e7p/ledmatrix/board_ledmatrix/ledmatrix.c

/*
	ledramp.c
	
	Copyright 2008, 2009 Michel Pollet <buserror@gmail.com>

 	This file is part of simavr.

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
	You should have received a copy of the GNU General Public License
	along with simavr.  If not, see <http://www.gnu.org/licenses/>.
 */

#include <stdlib.h>
#include <stdio.h>
#include <libgen.h>
#if __APPLE__
#include <GLUT/glut.h>
#else
#include <GL/glut.h>
#endif
#include <pthread.h>

#include "sim_avr.h"
#include "avr_ioport.h"
#include "sim_elf.h"
#include "sim_gdb.h"
#include "sim_vcd_file.h"

avr_t * avr = NULL;
avr_vcd_t vcd_file;
uint8_t	pin_state = 0;	// current port C
uint8_t	old_pin_state = 0; // old port C
#define WIDTH 200
#define HEIGHT 8
#define VERTICAL_REGISTERS 2
uint8_t register_bytes[VERTICAL_REGISTERS][WIDTH * HEIGHT / 8];
uint8_t redraw = 0;

float pixsize = 5;
int window;

/*
 * Shift Register helper function
 * shifts one array around one bit and appends value
 */
void shiftRegister(uint8_t *array, uint8_t value) {
	int len = (WIDTH * HEIGHT / 8) - 1;
	for(int i = 0; i < len; i++) {
		array[i] = (array[i] >> 1) | ((array[i+1] & 1) << 7);
	}
	array[len] = (array[len] >> 1) | (value > 0 ? 1 << 7: 0);
}

/*
 * called when the AVR change any of the pins on port C
 * so lets update our buffer
 */
void pin_changed_hook(struct avr_irq_t * irq, uint32_t value, void * param)
{
	pin_state = (pin_state & ~(1 << irq->irq)) | (value << irq->irq);
	// SCK is PC6
	if(!(old_pin_state & (1 << 6)) && (pin_state & (1 << 6))) {
		// we have to shift anything
		// DATA1 is PC2
		shiftRegister(register_bytes[0], pin_state & (1 << 2));
		// DATA2 is PC4
		shiftRegister(register_bytes[1], pin_state & (1 << 4));
	}
	// RCK is PC7
	if(!(old_pin_state & (1 << 7)) && (pin_state & (1 << 7))) {
		redraw = 1;
	}
	old_pin_state = pin_state;
}

void displayCB(void)		/* function called whenever redisplay needed */
{
	
	// OpenGL rendering goes here...
	glClear(GL_COLOR_BUFFER_BIT);

	// Set up modelview matrix
	glMatrixMode(GL_MODELVIEW); // Select modelview matrix
	glLoadIdentity(); // Start with an identity matrix

	float grid = pixsize;
	float size = grid * 0.8;
    glBegin(GL_QUADS);

	for (int di = 0; di < WIDTH; di++) {
		for (int reg = 0; reg < VERTICAL_REGISTERS; reg++) {
			uint8_t register_byte = register_bytes[reg][di];
			for (int si = 0; si < HEIGHT; si++) {
				char on = ((register_byte & (0x80 >> si)) != 0);
				if (on) {
					glColor3f(1,0.9f,0);
				} else {
					glColor3f(0.4f,0.3f,0);
				}
				float x = (di) * grid;
				float y = (si + reg * HEIGHT - VERTICAL_REGISTERS * HEIGHT + 1) * grid;
				glVertex2f(x + size, y + size);
				glVertex2f(x, y + size);
				glVertex2f(x, y);
				glVertex2f(x + size, y);
			}
		}
	}

    glEnd();
    glutSwapBuffers();
    //glFlush();				/* Complete any pending operations */
}

void keyCB(unsigned char key, int x, int y)	/* called on key press */
{
	if (key == 'q')
		exit(0);
	//static uint8_t buf[64];
	switch (key) {
		case 'q':
		case 0x1f: // escape
			exit(0);
			break;
		case 'r':
			printf("Starting VCD trace\n");
			avr_vcd_start(&vcd_file);
			break;
		case 's':
			printf("Stopping VCD trace\n");
			avr_vcd_stop(&vcd_file);
			break;
	}
}

// gl timer. if the pin have changed states, refresh display
void timerCB(int i)
{
	// restart timer
	glutTimerFunc(16, timerCB, 0);

	if (redraw == 1) {
		redraw = 0;
		glutPostRedisplay();
	}
}

static void * avr_run_thread(void * oaram)
{
	while (1) {
		avr_run(avr);
	}
	return NULL;
}


int main(int argc, char *argv[])
{
	elf_firmware_t f;
	const char * fname =  "atmega644_ledmatrix.axf";
	elf_read_firmware(fname, &f);

	printf("firmware %s f=%d mmcu=%s\n", fname, (int)f.frequency, f.mmcu);

	avr = avr_make_mcu_by_name(f.mmcu);
	if (!avr) {
		fprintf(stderr, "%s: AVR '%s' not known\n", argv[0], f.mmcu);
		exit(1);
	}
	avr_init(avr);
	avr_load_firmware(avr, &f);

	// initialize our 'peripheral'
	// connect all the pins on port B to our callback
	for (int i = 0; i < 8; i++)
		avr_irq_register_notify(
			avr_io_getirq(avr, AVR_IOCTL_IOPORT_GETIRQ('C'), i),
			pin_changed_hook, 
			NULL);

	// even if not setup at startup, activate gdb if crashing
	avr->gdb_port = 1234;
	if (0) {
		//avr->state = cpu_Stopped;
		avr_gdb_init(avr);
	}

	/*
	 *	VCD file initialization
	 *	
	 *	This will allow you to create a "wave" file and display it in gtkwave
	 *	Pressing "r" and "s" during the demo will start and stop recording
	 *	the pin changes
	 */
	avr_vcd_init(avr, "gtkwave_output.vcd", &vcd_file, 100000 /* usec */);
	avr_vcd_add_signal(&vcd_file, 
		avr_io_getirq(avr, AVR_IOCTL_IOPORT_GETIRQ('C'), IOPORT_IRQ_PIN_ALL), 8 /* bits */ ,
		"portc" );

	printf( "Demo launching: 'LED' matrix is SCK = PC6, DATA1 = PC2, DATA2 = PC4, RCK = PC7\n"
			"   Press 'q' to quit\n"
			"   Press 'r' to start recording a 'wave' file\n"
			"   Press 's' to stop recording\n"
			);

	/*
	 * OpenGL init, can be ignored
	 */
	glutInit(&argc, argv);		/* initialize GLUT system */

	glutInitDisplayMode(GLUT_RGB | GLUT_DOUBLE);
	glutInitWindowSize(WIDTH * pixsize, VERTICAL_REGISTERS * HEIGHT * pixsize);
	window = glutCreateWindow("LED Matrix");	/* create window */

	// Set up projection matrix
	glMatrixMode(GL_PROJECTION); // Select projection matrix
	glLoadIdentity(); // Start with an identity matrix
	glOrtho(0, WIDTH * pixsize, 0, VERTICAL_REGISTERS * HEIGHT * pixsize, 0, 10);
	glScalef(1,-1,1);
	glTranslatef(0, -1 * pixsize, 0);

	glutDisplayFunc(displayCB);		/* set window's display callback */
	glutKeyboardFunc(keyCB);		/* set window's key callback */
	glutTimerFunc(48, timerCB, 0);

	// the AVR run on it's own thread. it even allows for debugging!
	pthread_t run;
	pthread_create(&run, NULL, avr_run_thread, NULL);

	glutMainLoop();
}
