e7p/ledmatrix/nft/image.h

static uint16_t image[3][100] = {{
0x0000, 0x0000, 0x0000, 0x0000, 0x3ffe, 0x3ffe, 0x1f00, 0x07c0, 0x01f0, 0x007e,
0x3ffe, 0x3ffe, 0x0000, 0x0000, 0x3ffe, 0x3ffe, 0x3ffe, 0x318e, 0x318e, 0x318e,
0x300e, 0x0000, 0x0000, 0x3ffe, 0x3ffe, 0x318e, 0x318e, 0x318e, 0x300e, 0x000c,
0x0000, 0x3ffe, 0x3ffe, 0x3ffe, 0x300e, 0x300e, 0x380e, 0x3ffc, 0x1ffc, 0x07f0,
0x0000, 0x0000, 0x0000},{0x0000, 0x0000, 0x0000, 0x0000, 0x7ffe, 0x7ffe, 0x71c0, 0x71c0, 0x71c0, 0x71c0,
0x0000, 0x0000, 0x7ffc, 0x7ffe, 0x000e, 0x0006, 0x0006, 0x000c, 0x7ffe, 0x7ffe,
0x7ffe, 0x0000, 0x0000, 0x7ffe, 0x7ffe, 0x000e, 0x000e, 0x000e, 0x000e, 0x0000,
0x0000, 0x0000},{0x0000, 0x0000, 0x0000, 0x3000, 0x3000, 0x3000, 0x3ffe, 0x3ffe, 0x3ffe, 0x3000,
0x3000, 0x0000, 0x3ffe, 0x3ffe, 0x3ffe, 0x0380, 0x0380, 0x0380, 0x3ffe, 0x3ffe,
0x3ffe, 0x0000, 0x0000, 0x3006, 0x3ffe, 0x3ffe, 0x3ffe, 0x3006, 0x0000, 0x3ffe,
0x3ffe, 0x3ffe, 0x1f80, 0x07e0, 0x01f8, 0x007e, 0x3ffe, 0x3ffe, 0x0000, 0x0000,
0x07f8, 0x1ffc, 0x1ffe, 0x380e, 0x3006, 0x31c6, 0x31fc, 0x31fe, 0x31fe, 0x0000,
0x0004, 0x0f0e, 0x1f8e, 0x3f86, 0x3bc6, 0x31ce, 0x39fe, 0x38fc, 0x1078, 0x0000,
0x0000, 0x0000}};
